rixth/aurai/software/ac.js

var EventEmitter = require('events').EventEmitter,
    SerialPort = require('serialport'),
    bufferParser = require('./buffer-parser'),
    util = require('util');

function AC(serialPort) {
  this.running = false;
  this.temp = null;
  this.mode = null;
  this.fanSpeed = null;
  this.environment = {};
  this.resetTimer;
  this.serialPortPath = serialPort;
  // this.firePortCycleTimer();
  this.queue = [];

  this.serialPort = new SerialPort.SerialPort(this.serialPortPath, {
    baudrate: 9600,
    parser: bufferParser()
  });

  this.serialPort.on('data', function (data) {
    console.log('Got', data);

    if (!this.lastCallback) {
      return console.error('No one to give this data to?');
    }

    // data[0] = CMD_OK/FAIL
    // data[1] = SEND_OK/FAIL
    // data[2] = RESP_OK/TO
    // data[3] = SIZE
    // data[4..4+SIZE] = DATA

    if (data[0] != 0x03) {
      var error = 'Command rejected by hub';
      return this.lastCallback(error);
    }

    if (data[1] != 0x01) {
      var error = 'Transmission from hub to spoke failed';
      return this.lastCallback(error);
    }

    if (data[2] != 0x04) {
      var error = 'Spoke did not respond after command was sent';
      return this.lastCallback(error);
    }

    console.log('Got', data[3], 'bytes back from spoke');

    this.lastCallback(false, data.slice(4));
  }.bind(this));
}


AC.prototype = Object.create(EventEmitter.prototype);

AC.prototype.firePortCycleTimer = function () {
  var hadPort = !!this.serialPort;
  if (this.serialPort) {
    this.serialPort.close();
  }
  this.serialPort = new SerialPort.SerialPort(this.serialPortPath, {
    baudrate: 9600,
    parser: bufferParser(false)
  });
  if (hadPort) {
    this.serialPort.open();
  }
  setTimeout(this.firePortCycleTimer.bind(this), 60000);
};

AC.prototype.status = function () {
  return {
    running: this.running,
    mode: this.mode,
    fanSpeed: this.fanSpeed,
    temp: this.temp,
    environment: this.environment
  };
};

AC.prototype._basicResponseParse = function (cb, err, payload, finalCb) {
  delete this.lastCallback;

  if (err) {
    console.error(err);
    return cb(false);
  } else if (payload[0] == 0x01 || payload[0] == 0x04) {
    // SPOKE_RESP_OK / SPOKE_RESP_STATUS
    this._parseState(payload.slice(1));
    return cb(true);
  } else if (payload[0] == 0x02) {
    // SPOKE_RESP_FAIL
    console.error('Spoke rejected the command');
    return cb(false);
  } else {
    if (finalCb) {
      // Someone wants the data. It's their problem now.
      return finalCb(payload);
    } else {
      console.error('Cannot process payload', payload);
    }
  }
}

AC.prototype.power = function (mode, cb) {
  this._sendCmd(commands.power[mode], this._basicResponseParse.bind(this, cb));
};

AC.prototype.reset = function (cb) {
  this._sendCmd(commands.reset, this._basicResponseParse.bind(this, cb));
};

AC.prototype.environmentLog = function (count, cb) {
  var buffer = new Buffer(2);
  buffer.writeUInt8(0x02, 0);
  buffer.writeUInt8(count, 1);
  this._sendCmd(buffer, function (err, payload) {
    this._basicResponseParse(cb, err, payload, function (data) {
      var humidity = [];
      var temperature = [];
      for (var i = 0; i < data.length; i += 2) {
        humidity.push(data.readUInt8(i));
        temperature.push(data.readInt8(i + 1));
      }
      cb(true, {
        humidity: humidity,
        temperature: temperature
      });
    }.bind(this));
  }.bind(this));
}

AC.prototype.environmentFromChip = function (cb) {
  this._sendCmd(commands.environment, function (err, payload) {
    this._basicResponseParse(cb, err, payload, function (data) {
      if (data.readUInt8(0) != 0x08) {
        return cb(false);
      }

      cb(true, {
        humidity: data.readUInt8(1),
        temperature: data.readInt8(2)
      });
    }.bind(this));
  }.bind(this));
};

AC.prototype.statusFromChip = function (cb) {
  this._sendCmd(commands.status, this._basicResponseParse.bind(this, cb));
};

AC.prototype.tempUp = function (cb) {
  this._sendCmd(commands.temperature.up, this._basicResponseParse.bind(this, cb));
};

AC.prototype.tempDown = function (cb) {
  this._sendCmd(commands.temperature.down, this._basicResponseParse.bind(this, cb));
};

AC.prototype.tempExact = function (temp, cb) {
  var buffer = new Buffer(3);
  buffer.writeUInt8(0x01, 0);
  buffer.writeUInt8(commands.temperature.exact, 1);
  buffer.writeUInt8(temp, 2);
  this._sendCmd(buffer, this._basicResponseParse.bind(this, cb));
};

AC.prototype.setFanSpeed = function (speed, cb) {
  this._sendCmd(commands.fanSpeed[speed], this._basicResponseParse.bind(this, cb));
};

AC.prototype.setPowerTimer = function (onOrOff, hours, cb) {
  var buffer = new Buffer(3);
  buffer.writeUInt8(0x01, 0);
  buffer.writeUInt8(commands.timer[onOrOff], 1);
  buffer.writeUInt8(hours, 2);
  this._sendCmd(buffer, this._basicResponseParse.bind(this, cb));
};

AC.prototype.setMode = function (mode, cb) {
  this._sendCmd(commands.mode[mode], this._basicResponseParse.bind(this, cb));
};

AC.prototype._sendCmd = function (bits, cb) {
  if (this.lastCallback) {
    return this.queue.push(arguments);
  }

  var buf;

  if (Buffer.isBuffer(bits)) {
    // Prefix with the number of bytes
    var dataBuf = bits;
    buf = new Buffer(dataBuf.length + 1);
    buf.writeUInt8(dataBuf.length, 0);
    dataBuf.copy(buf, 1);
  } else if (typeof bits === 'number') {
    buf = new Buffer(3);
    buf.writeUInt8(0x02, 0);
    buf.writeUInt8(0x01, 1);
    buf.writeUInt8(bits, 2);
  } else if (Array.isArray(bits)) {
    buf = new Buffer(bits.length + 1);
    buf.writeUInt8(bits.length, 0);
    bits.forEach(function (bit, idx) {
      buf.writeUInt8(bit, idx + 1);
    });
  } else {
    throw new Error("don't know what to do with " + bits);
  }

  this.lastCallback = function () {
    cb.apply(this, arguments);
    if (this.queue.length) {
      args = this.queue.shift();
      console.log(args);
      this._sendCmd.apply(this, args);
    }
  }.bind(this);

  console.log('Writing', buf, 'to serial port');

  this.serialPort.write(buf, function (_err) {
    if (_err && this.lastCallback) {
      this.lastCallback("Serial error", []);
      this.lastCallback = null;
    }
  }.bind(this));
}

AC.prototype._parseState = function (buffer) {
  var statusInt = buffer.readUInt16BE(0);
  this.temp = statusInt & 0xFF;
  this.fanSpeed = FAN_SPEEDS[((3 << 8) & statusInt) >> 8];
  this.mode = MODES[((3 << 10) & statusInt) >> 10];
  this.running = !!((1 << 12) & statusInt);
}

AC.prototype.init = function (cb) {
  this.serialPort.open(cb);
};

var commands = {
  power: {
    toggle: 0x08,
    on: 0x08 | 1,
    off: 0x08 | 2
  },
  mode: {
    next: 0x10,
    cool: 0x10 | 1,
    energySaver: 0x10 | 2,
    dry: 0x10 | 3,
    fan: 0x10 | 4
  },
  fanSpeed: {
    next: 0x18,
    low: 0x18 | 1,
    medium: 0x18 | 2,
    high: 0x18 | 3
  },
  temperature: {
    up: 0x20,
    down: 0x21,
    exact: 0x28
  },
  status: 0x30,
  reset: 0x50,
  environment: 0x48
};



var MODES = [
  'COOL',
  'ENERGY_SAVER',
  'FAN',
  'DRY'
];

var FAN_SPEEDS = [
  'LOW',
  'MED',
  'HIGH'
]

module.exports = AC;
