rixth/aurai/firmware/hub/src/CommandLine.h

void CommandLine_start();
void CommandLine_subcommandPower();
void CommandLine_subcommandTemperature();
void CommandLine_subcommandMode();
void CommandLine_subcommandFanSpeed();
void CommandLine_subcommandReset();
void CommandLine_subcommandDumpLog();
void CommandLine_subcommandStatus();
void CommandLine_subcommandEnvironment();
void CommandLine__handleBasicCommand(uint8_t* payload, uint8_t len);
void CommandLine__waitForResponse();
